Anjanamb/Smart-Restaurant-POS-system-SafEat/Enclosure/#/18650.jpg

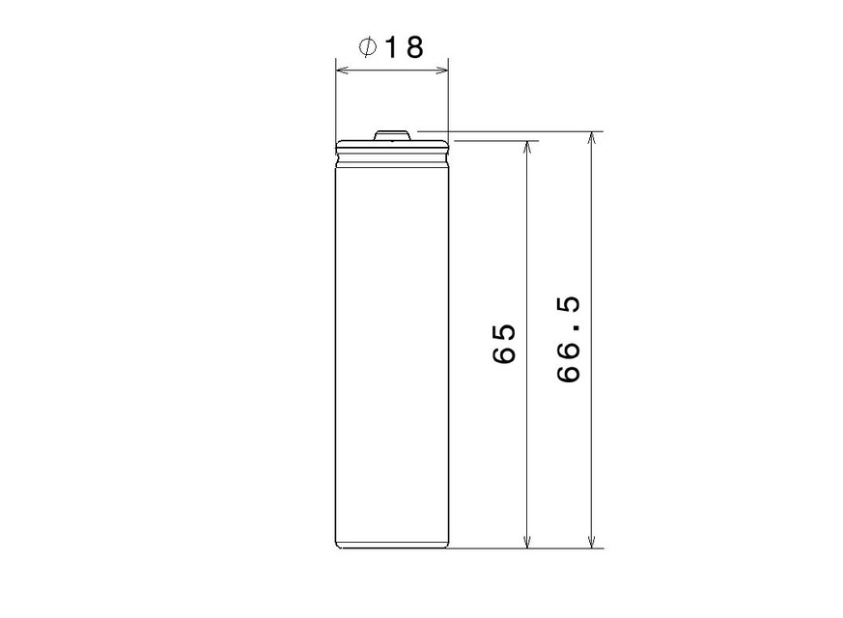
Enclosure/#/18650.jpg
