Anjanamb/Smart-Restaurant-POS-system-SafEat/Enclosure/Switch 2/SPDT.JPG

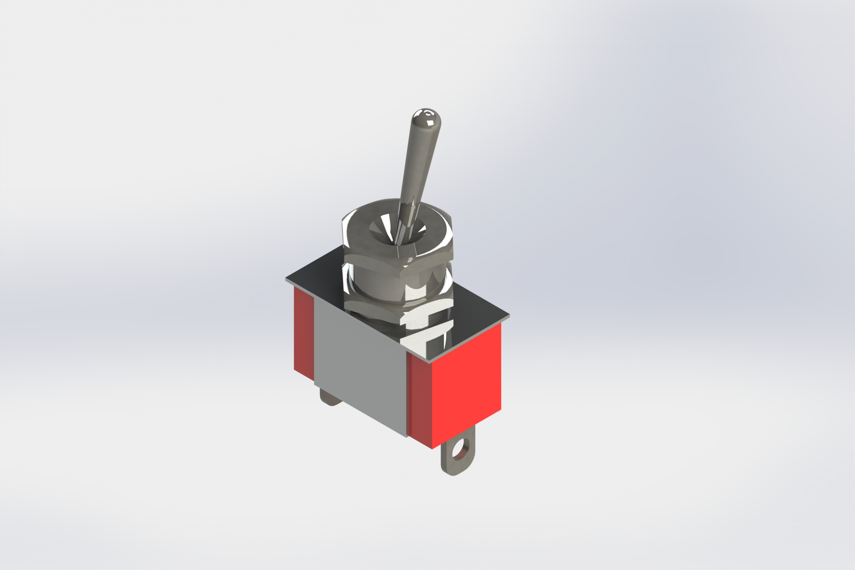
Enclosure/Switch 2/SPDT.JPG
