Anjanamb/Smart-Restaurant-POS-system-SafEat/Enclosure/Switch/Switch I 0.JPG

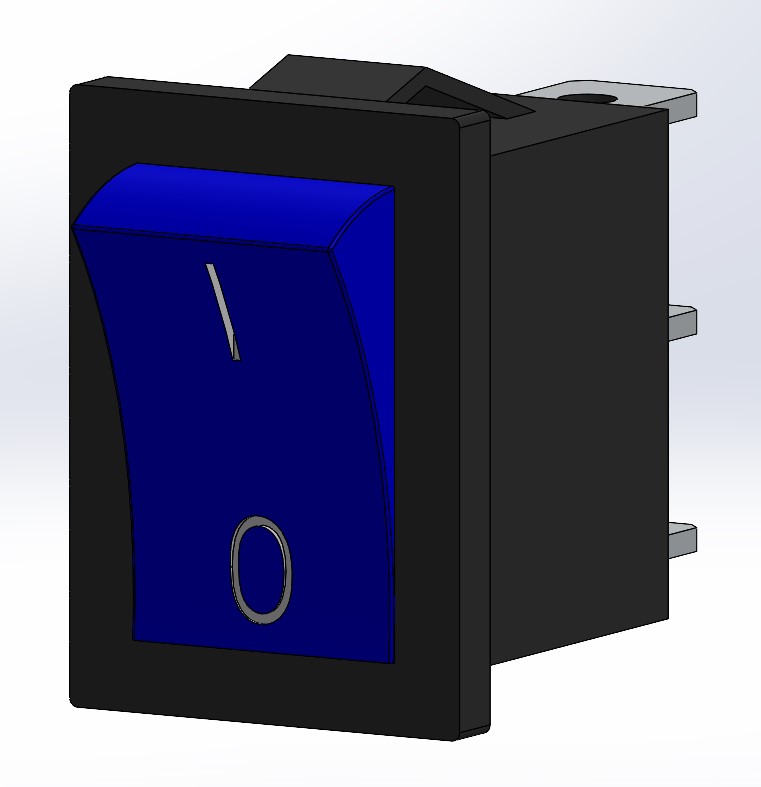
Enclosure/Switch/Switch I 0.JPG
