Anjanamb/Smart-Restaurant-POS-system-SafEat/Charging module/3D body step files/SOIC 8/8SIOC.stp

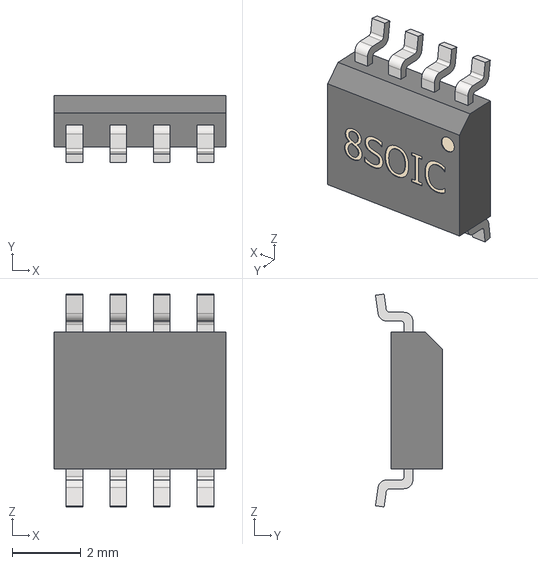
[picture p23: CAD file, 2022-06-12]
Charging module/3D body step files/SOIC 8/8SIOC.stp
5.00 x 1.95 x 6.20 mm
8SOIC_BODY
8SOIC_PIN x 8
