Anjanamb/Smart-Restaurant-POS-system-SafEat/Charging module/3D body step files/SOT 23-6/sot-23-6.stp

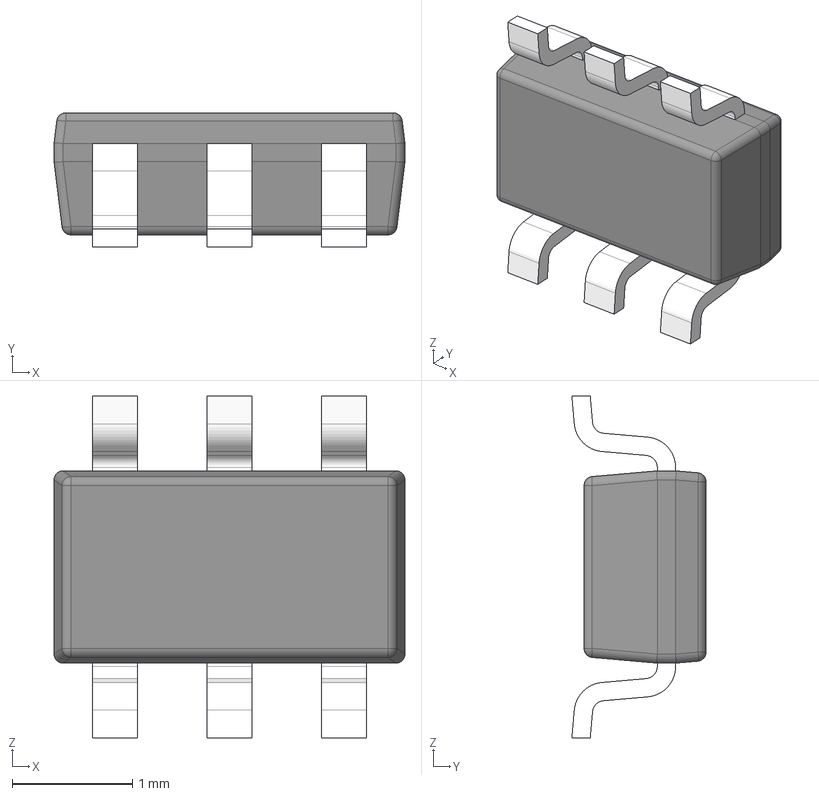
[picture p24: CAD file, 2022-06-12]
Charging module/3D body step files/SOT 23-6/sot-23-6.stp
2.92 x 1.12 x 2.84 mm
BODY_MF06A
LEAD_MF06A x 6
