Anjanamb/Smart-Restaurant-POS-system-SafEat/Charging module/3D body step files/TSSOP-8/tssop8_model.STEP

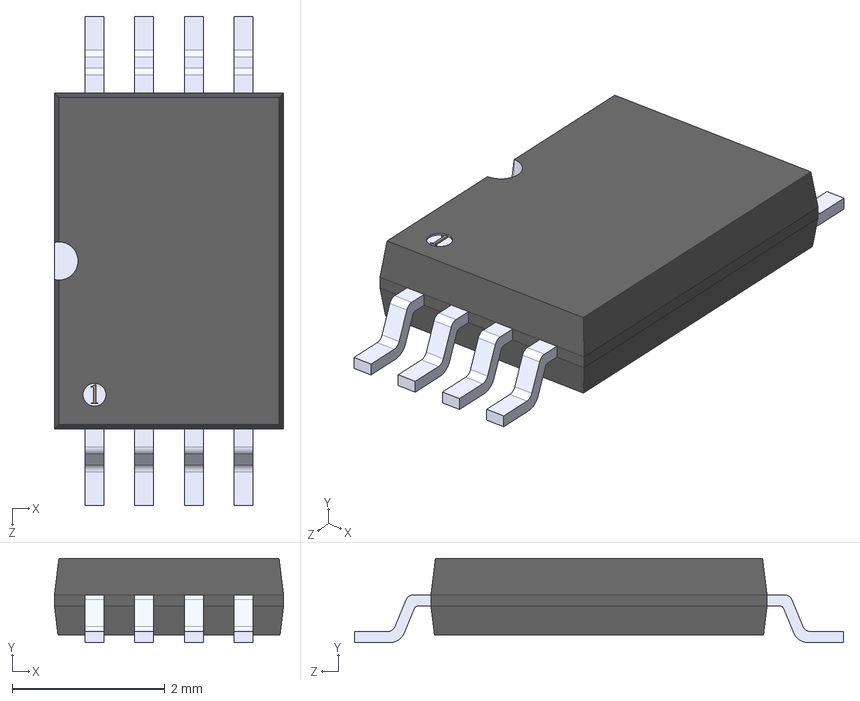
[picture p25: CAD file, 2022-06-12]
Charging module/3D body step files/TSSOP-8/tssop8_model.STEP
3.00 x 1.10 x 6.40 mm
tssop8_body
pin5to8_tssop8 x 8
