Anjanamb/Smart-Restaurant-POS-system-SafEat/Enclosure/#/keystone-electronics-18650-dual-cell-holder-pth-1.snapshot.1/keystone-PN1048.STEP

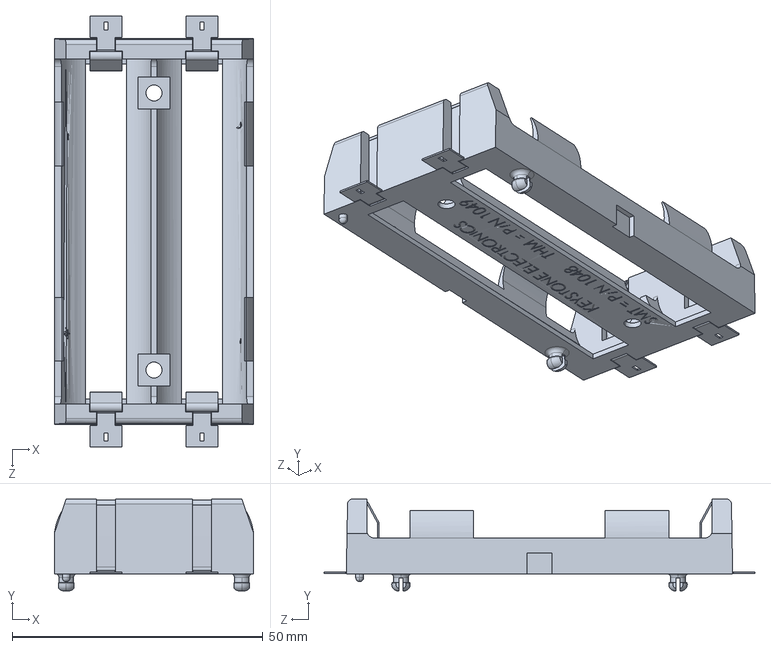
[picture p26: CAD file, 2022-06-12]
Enclosure/#/keystone-electronics-18650-dual-cell-holder-pth-1.snapshot.1/keystone-PN1048.STEP
39.8 x 18.3 x 86.0 mm
