Anjanamb/Smart-Restaurant-POS-system-SafEat/Enclosure/LED/5MM LED RED.step

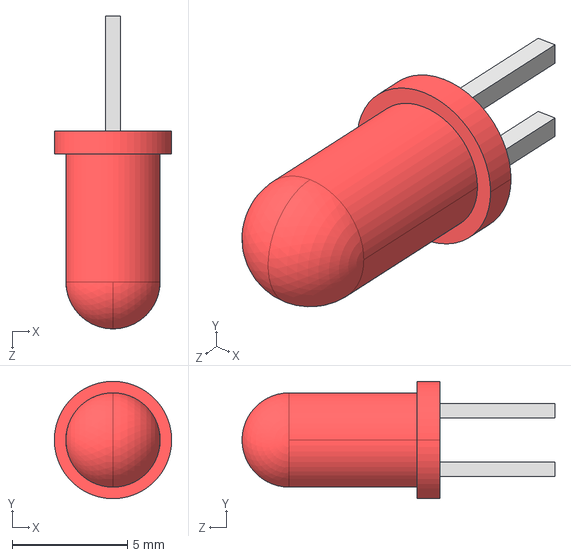
[picture p27: CAD file, 2022-06-26]
Enclosure/LED/5MM LED RED.step
5.10 x 5.10 x 13.6 mm
