Anjanamb/Smart-Restaurant-POS-system-SafEat/Enclosure/Switch 2/SPDT switch.SLDPRT

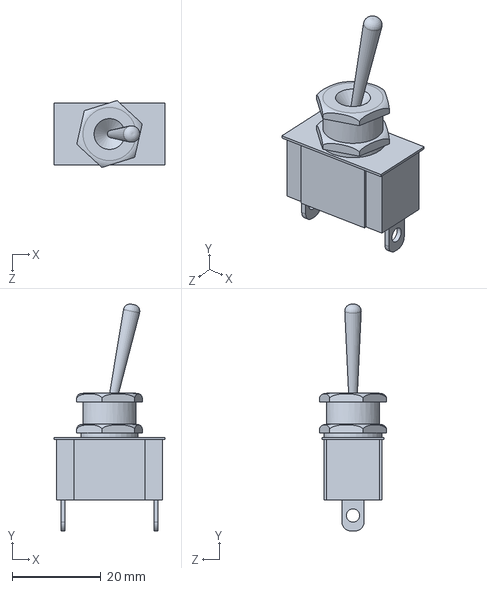
[picture p28: CAD file, 2022-06-26]
Enclosure/Switch 2/SPDT switch.SLDPRT
25.0 x 51.2 x 15.1 mm
