Anjanamb/Smart-Restaurant-POS-system-SafEat/Enclosure/Switch/Vypínač I 0.SLDPRT

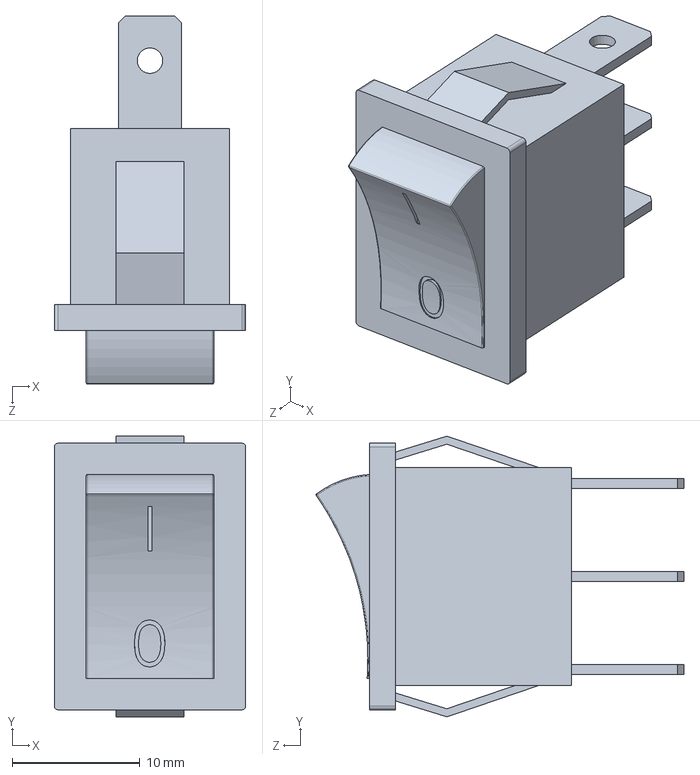
[picture p29: CAD file, 2022-06-26]
Enclosure/Switch/Vypínač I 0.SLDPRT
15.0 x 22.0 x 28.8 mm
