Anjanamb/Smart-Restaurant-POS-system-SafEat/Enclosure/Top.SLDPRT

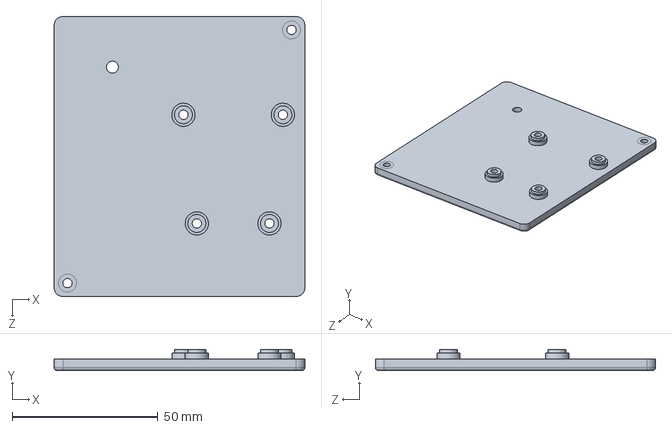
[picture p30: CAD file, 2022-06-26]
Enclosure/Top.SLDPRT
86.0 x 7.25 x 96.0 mm
