Anjanamb/Smart-Restaurant-POS-system-SafEat/Enclosure/Base.SLDPRT

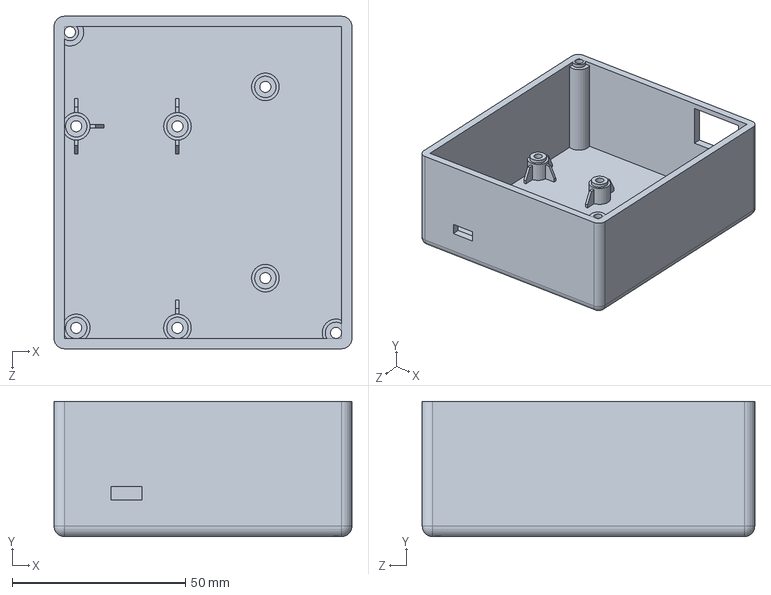
[picture p31: CAD file, 2022-06-26]
Enclosure/Base.SLDPRT
86.0 x 39.0 x 96.0 mm
