Anjanamb/Smart-Restaurant-POS-system-SafEat/Enclosure/RC522 RFID.STEP

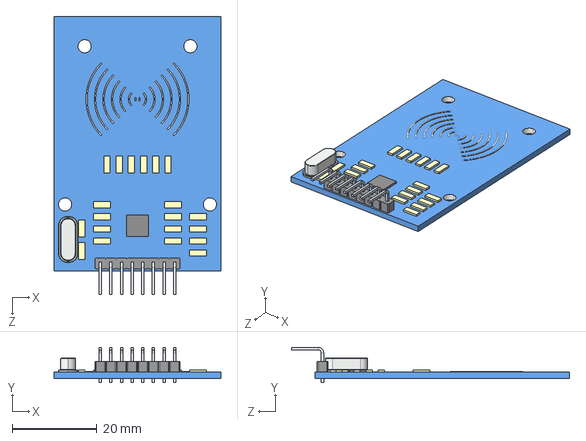
[picture p32: CAD file, 2022-06-12]
Enclosure/RC522 RFID.STEP
39.2 x 8.30 x 65.5 mm
